SebastianOberschwendtner/OTP20_oBank/04_Hardware/20_COTS/USB_C_Connector_Wuerth.FCStd

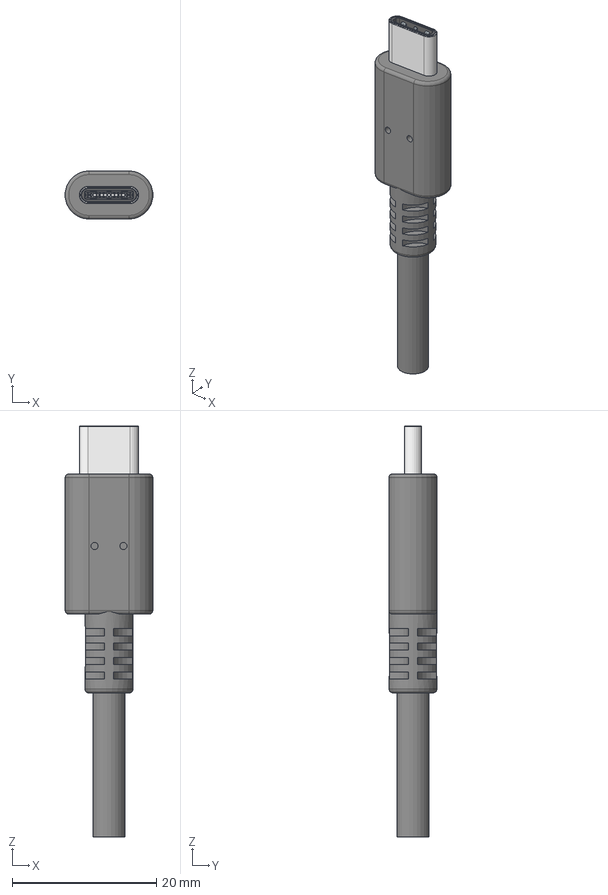
[picture p15: CAD file, 2022-06-06]
04_Hardware/20_COTS/USB_C_Connector_Wuerth.FCStd
12.2 x 6.70 x 57.0 mm
632712000112_Shelding
632712000112_Housing1
632712000112_Housing2
632712000112_Pin
632712000112_Pin001
632712000112_Pin002
632712000112_Pin003
632712000112_Pin004
632712000112_Pin005
632712000112_Pin006
632712000112_Pin007
632712000112_Pin008
632712000112_Pin009
632712000112_Pin010
632712000112_Pin011
632712000112_Shelding2.asm
632712000112_Shelding3.asm
632712000112_Shelding2.asm001
632712000112_Housing003
632712000112_Pin012
632712000112_Pin013
632712000112_Pin014
632712000112_Pin015
632712000112_Pin016
632712000112_Pin017
632712000112_Pin018
632712000112_Pin019
632712000112_Pin020
632712000112_Pin021
632712000112_Pin022
632712000112_Pin023
632712000112_Mylar
632712000112_Mylar001
