SebastianOberschwendtner/OTP20_oBank/04_Hardware/20_COTS/Battery_Contact_Flat.FCStd

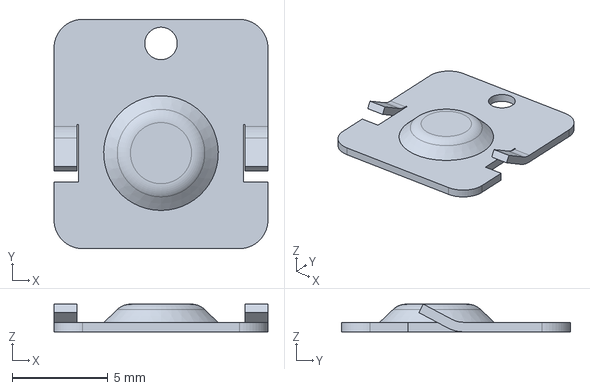
[picture p16: CAD file, 2022-06-06]
04_Hardware/20_COTS/Battery_Contact_Flat.FCStd
11.2 x 12.0 x 1.45 mm
