SebastianOberschwendtner/OTP20_oBank/04_Hardware/20_COTS/USB_A_Connector_Wuerth.FCStd

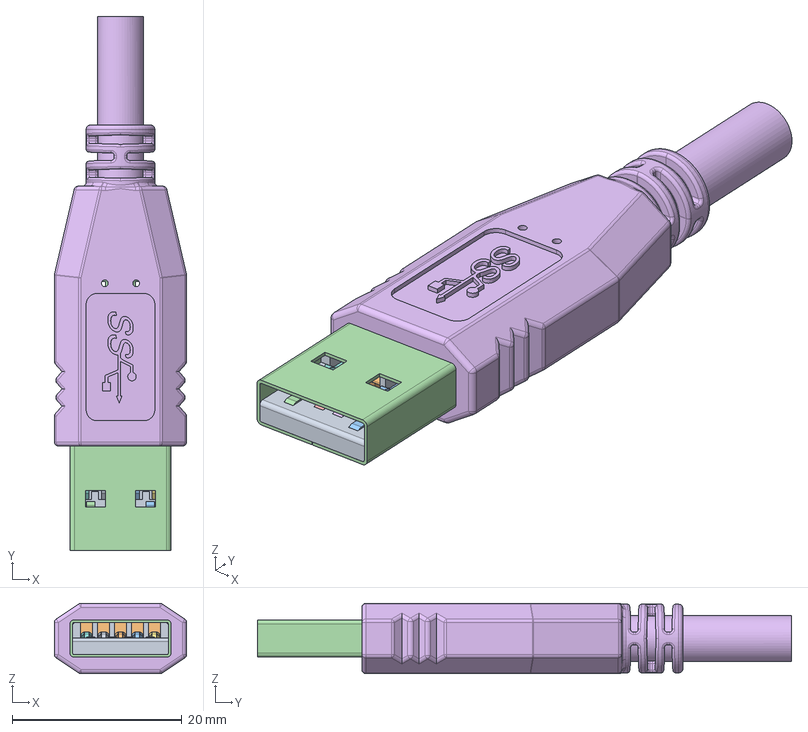
[picture p17: CAD file, 2022-06-06]
04_Hardware/20_COTS/USB_A_Connector_Wuerth.FCStd
15.6 x 62.9 x 8.30 mm
692901100001_BIS
692901100001_Dte_Lge
692901100001_Dte_Lge001
692901100001_Dte_Crt
692901100001_Dte_Crt001
692901100001_Crb
692901100001_Crb001
692901100001_Crb002
692901100001_Crb003
692901100001_Crb004
692901100001_Bis
692901100001_Surmoulage
