SebastianOberschwendtner/OTP20_oBank/04_Hardware/20_COTS/Lightpipe_Mentor_1282-2000.FCStd

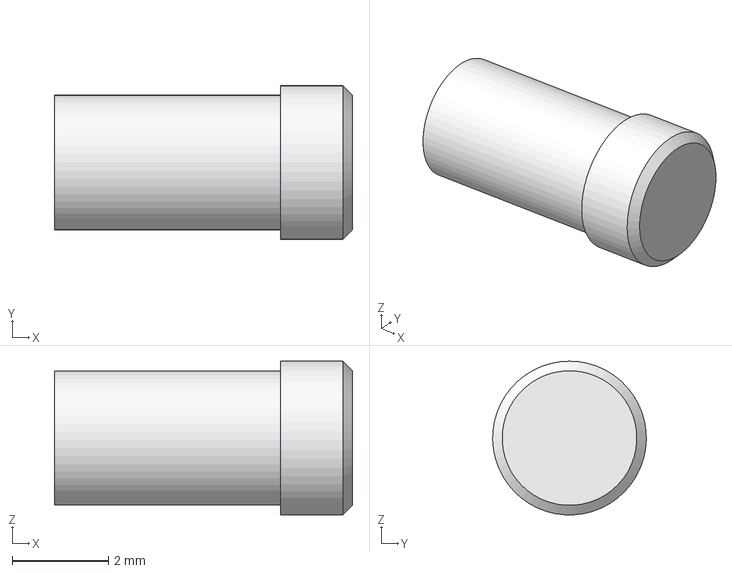
[picture p18: CAD file, 2021-10-10]
04_Hardware/20_COTS/Lightpipe_Mentor_1282-2000.FCStd
6.20 x 3.20 x 3.20 mm
