SebastianOberschwendtner/OTP20_oBank/04_Hardware/20_COTS/Lightpipe_Mentor_1271-1001.FCStd

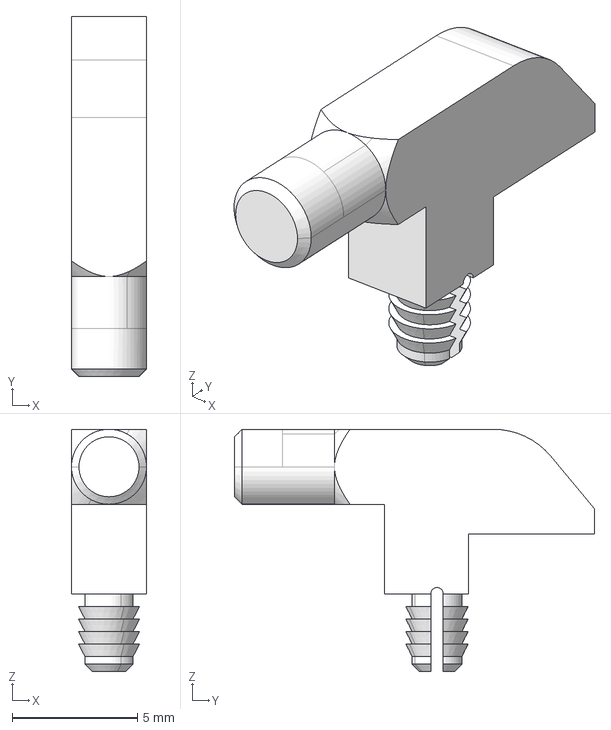
[picture p19: CAD file, 2021-10-10]
04_Hardware/20_COTS/Lightpipe_Mentor_1271-1001.FCStd
3.00 x 14.4 x 9.70 mm
