SebastianOberschwendtner/OTP20_oBank/04_Hardware/20_COTS/EA_W064048.FCStd

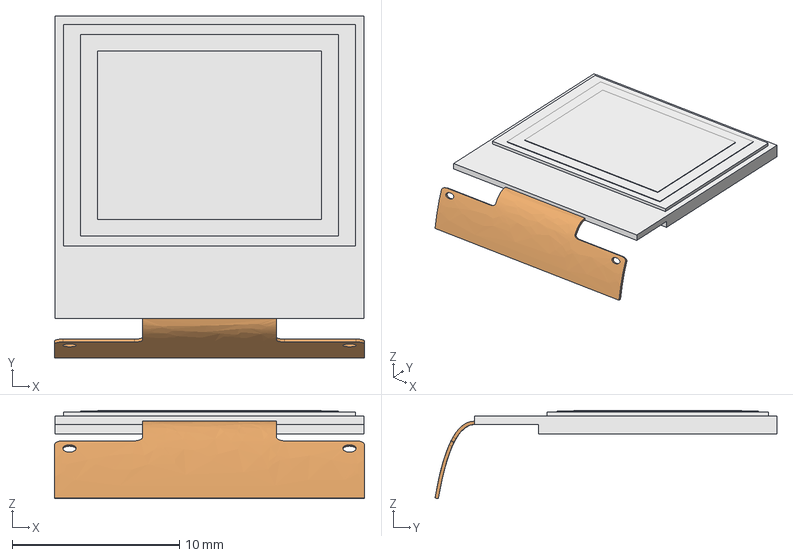
[picture p20: CAD file, 2021-07-01]
04_Hardware/20_COTS/EA_W064048.FCStd
18.6 x 20.5 x 5.28 mm
Display
Sketch_On_Surface
